julienrat/Norns_Fork/norns_fork_pcb/images/PXL_20220614_091723372.jpg

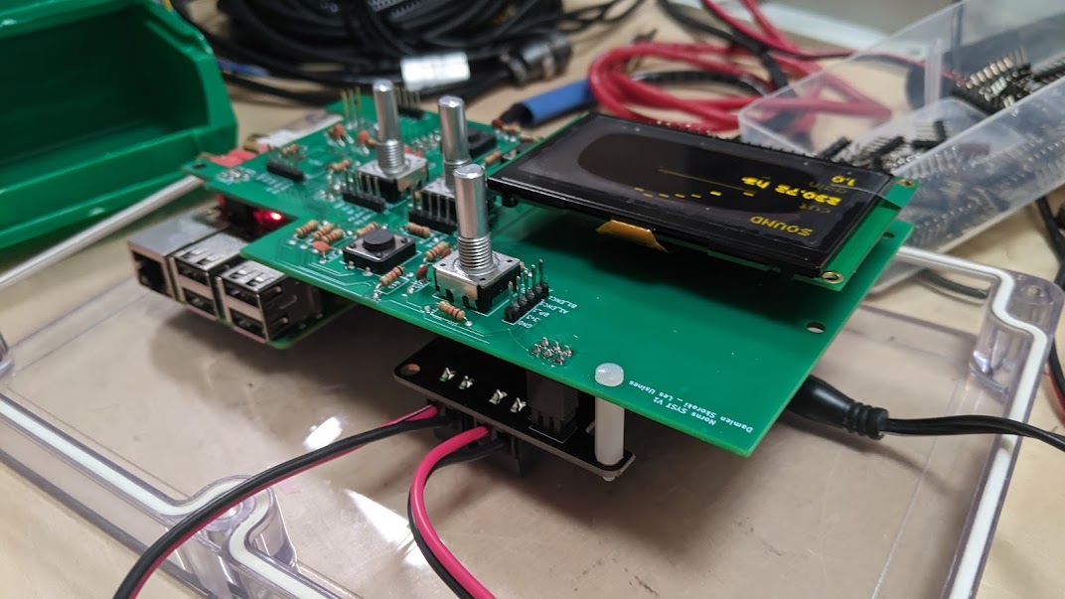
norns_fork_pcb/images/PXL_20220614_091723372.jpg
