julienrat/Norns_Fork/norns_fork_pcb/norns_EKO_kicad_sources/norns_eko_3.png

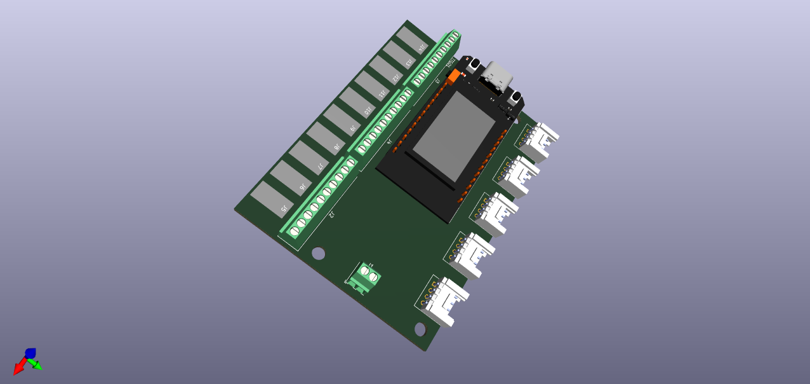
norns_fork_pcb/norns_EKO_kicad_sources/norns_eko_3.png
