julienrat/Norns_Fork/norns_fork_pcb/norns_EKO_kicad_sources/footprint/ttgo-tdisplay-kicad-master/microusb.SLDPRT

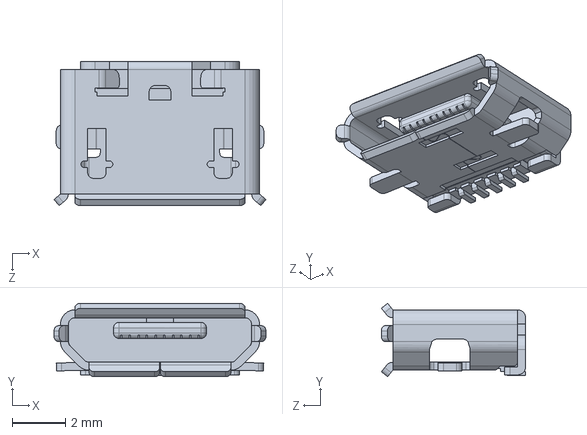
[picture p25: CAD file, 2022-07-06]
norns_fork_pcb/norns_EKO_kicad_sources/footprint/ttgo-tdisplay-kicad-master/microusb.SLDPRT
7.98 x 2.76 x 5.43 mm
