julienrat/Norns_Fork/norns_fork_pcb/norns_SYST_kicad_sources/edgecut/norns_fork-Edge_Cutsrnd.dxf

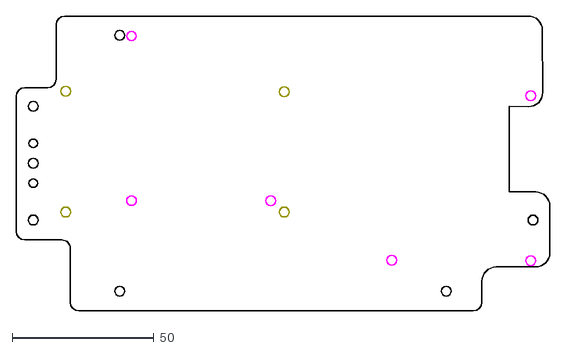
[picture p26: CAD file, 2022-07-06]
norns_fork_pcb/norns_SYST_kicad_sources/edgecut/norns_fork-Edge_Cutsrnd.dxf
187.9 x 103.8
