julienrat/Norns_Fork/norns_fork_pcb/norns_SYST_kicad_sources/footprint/Enc_Bourns_PEC11R-4015F-N0024/ecran.step

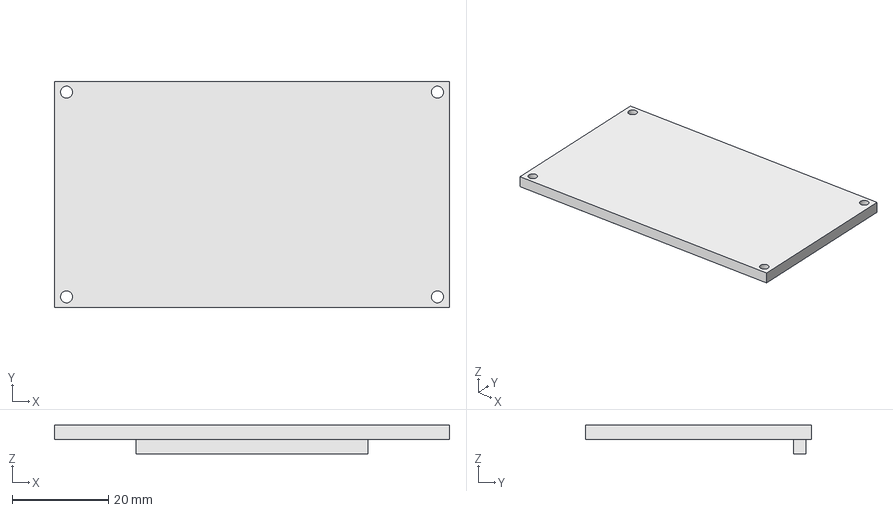
[picture p27: CAD file, 2022-06-02]
norns_fork_pcb/norns_SYST_kicad_sources/footprint/Enc_Bourns_PEC11R-4015F-N0024/ecran.step
82.0 x 47.0 x 6.00 mm
