julienrat/Norns_Fork/norns_fork_pcb/norns_SYST_kicad_sources/footprint/rb85p12_24.step

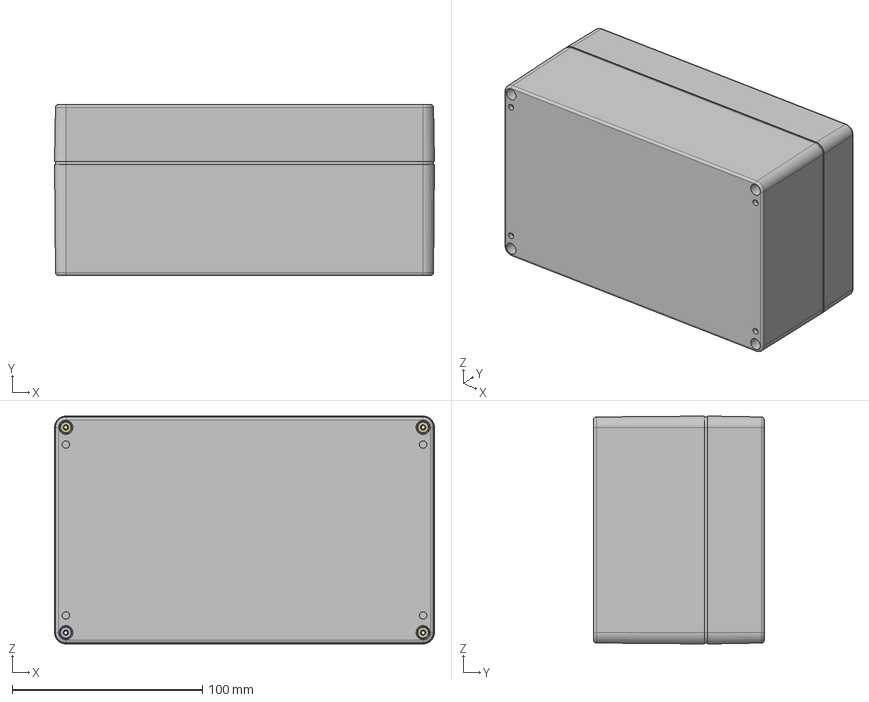
[picture p28: CAD file, 2022-07-06]
norns_fork_pcb/norns_SYST_kicad_sources/footprint/rb85p12_24.step
200.0 x 90.0 x 120.0 mm
RB85X24Y_RevA(Default)
RB85-X12Y_RevA
6102_4-40_threaded insert x 4
6032 4-40 Torx X 1.75_ Rev A x 4
8085 RB85 O Ring Rev A
