julienrat/Norns_Fork/3D_case/3D_case_syst_freecad/entretoises.FCStd

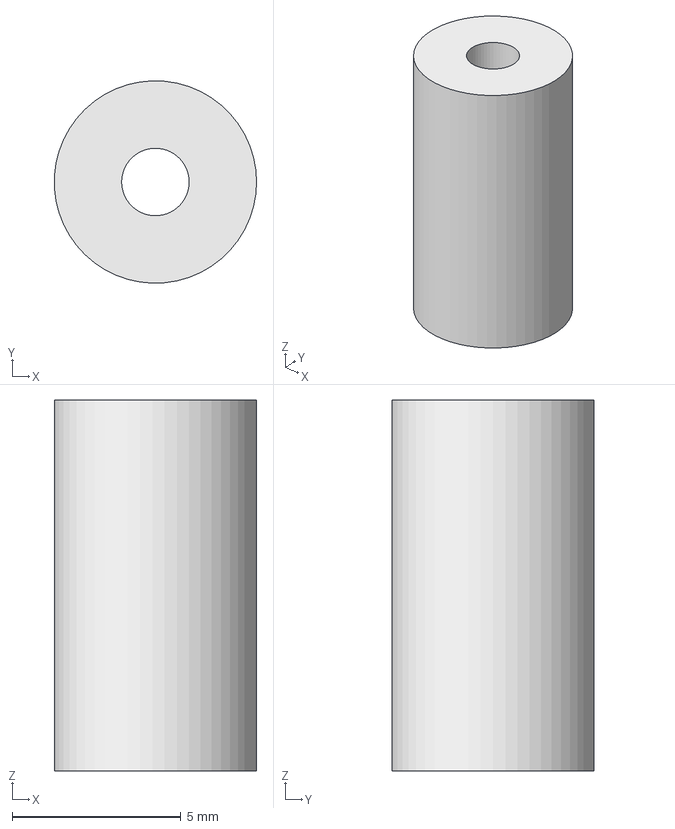
[picture p29: CAD file, 2022-06-15]
3D_case/3D_case_syst_freecad/entretoises.FCStd
5.99 x 6.00 x 11.0 mm
