julienrat/Norns_Fork/norns_fork_pcb/norns_SYST_kicad_sources/edgecut/#Fond boite.dxf

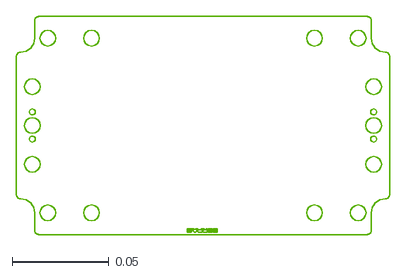
[picture p30: CAD file, 2022-07-06]
norns_fork_pcb/norns_SYST_kicad_sources/edgecut/#Fond boite.dxf
0.192 x 0.112
