julienrat/Norns_Fork/norns_fork_pcb/norns_SYST_kicad_sources/footprint/RASPBERRY PI 3.STEP

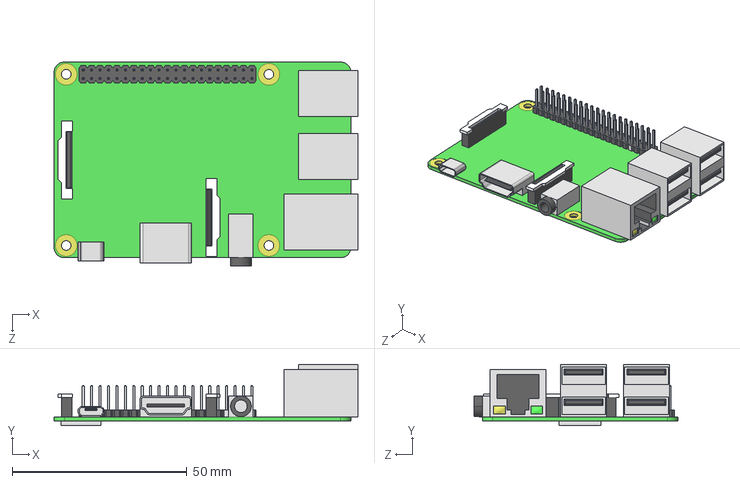
[picture p31: CAD file, 2022-06-15]
norns_fork_pcb/norns_SYST_kicad_sources/footprint/RASPBERRY PI 3.STEP
87.0 x 17.5 x 58.4 mm
