julienrat/Norns_Fork/norns_fork_pcb/norns_SYST_kicad_sources/edgecut/Norns_edgecut_final.dxf

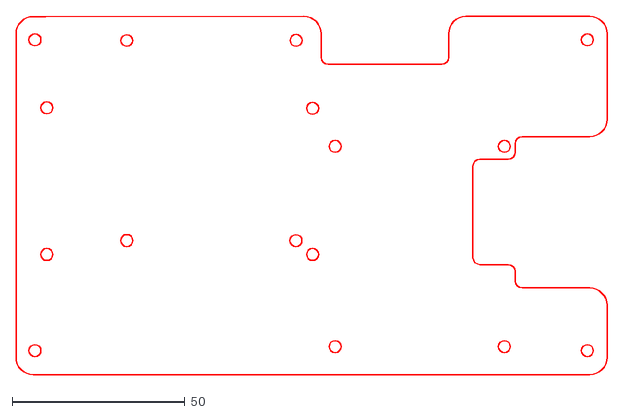
[picture p32: CAD file, 2022-07-01]
norns_fork_pcb/norns_SYST_kicad_sources/edgecut/Norns_edgecut_final.dxf
171.2 x 103.8
