julienrat/Norns_Fork/norns_fork_pcb/norns_SYST_kicad_sources/norns_fork.kicad_sch

## KiCad design norns_fork_pcb/norns_SYST_kicad_sources/norns_fork.kicad_sch (2022-07-01)

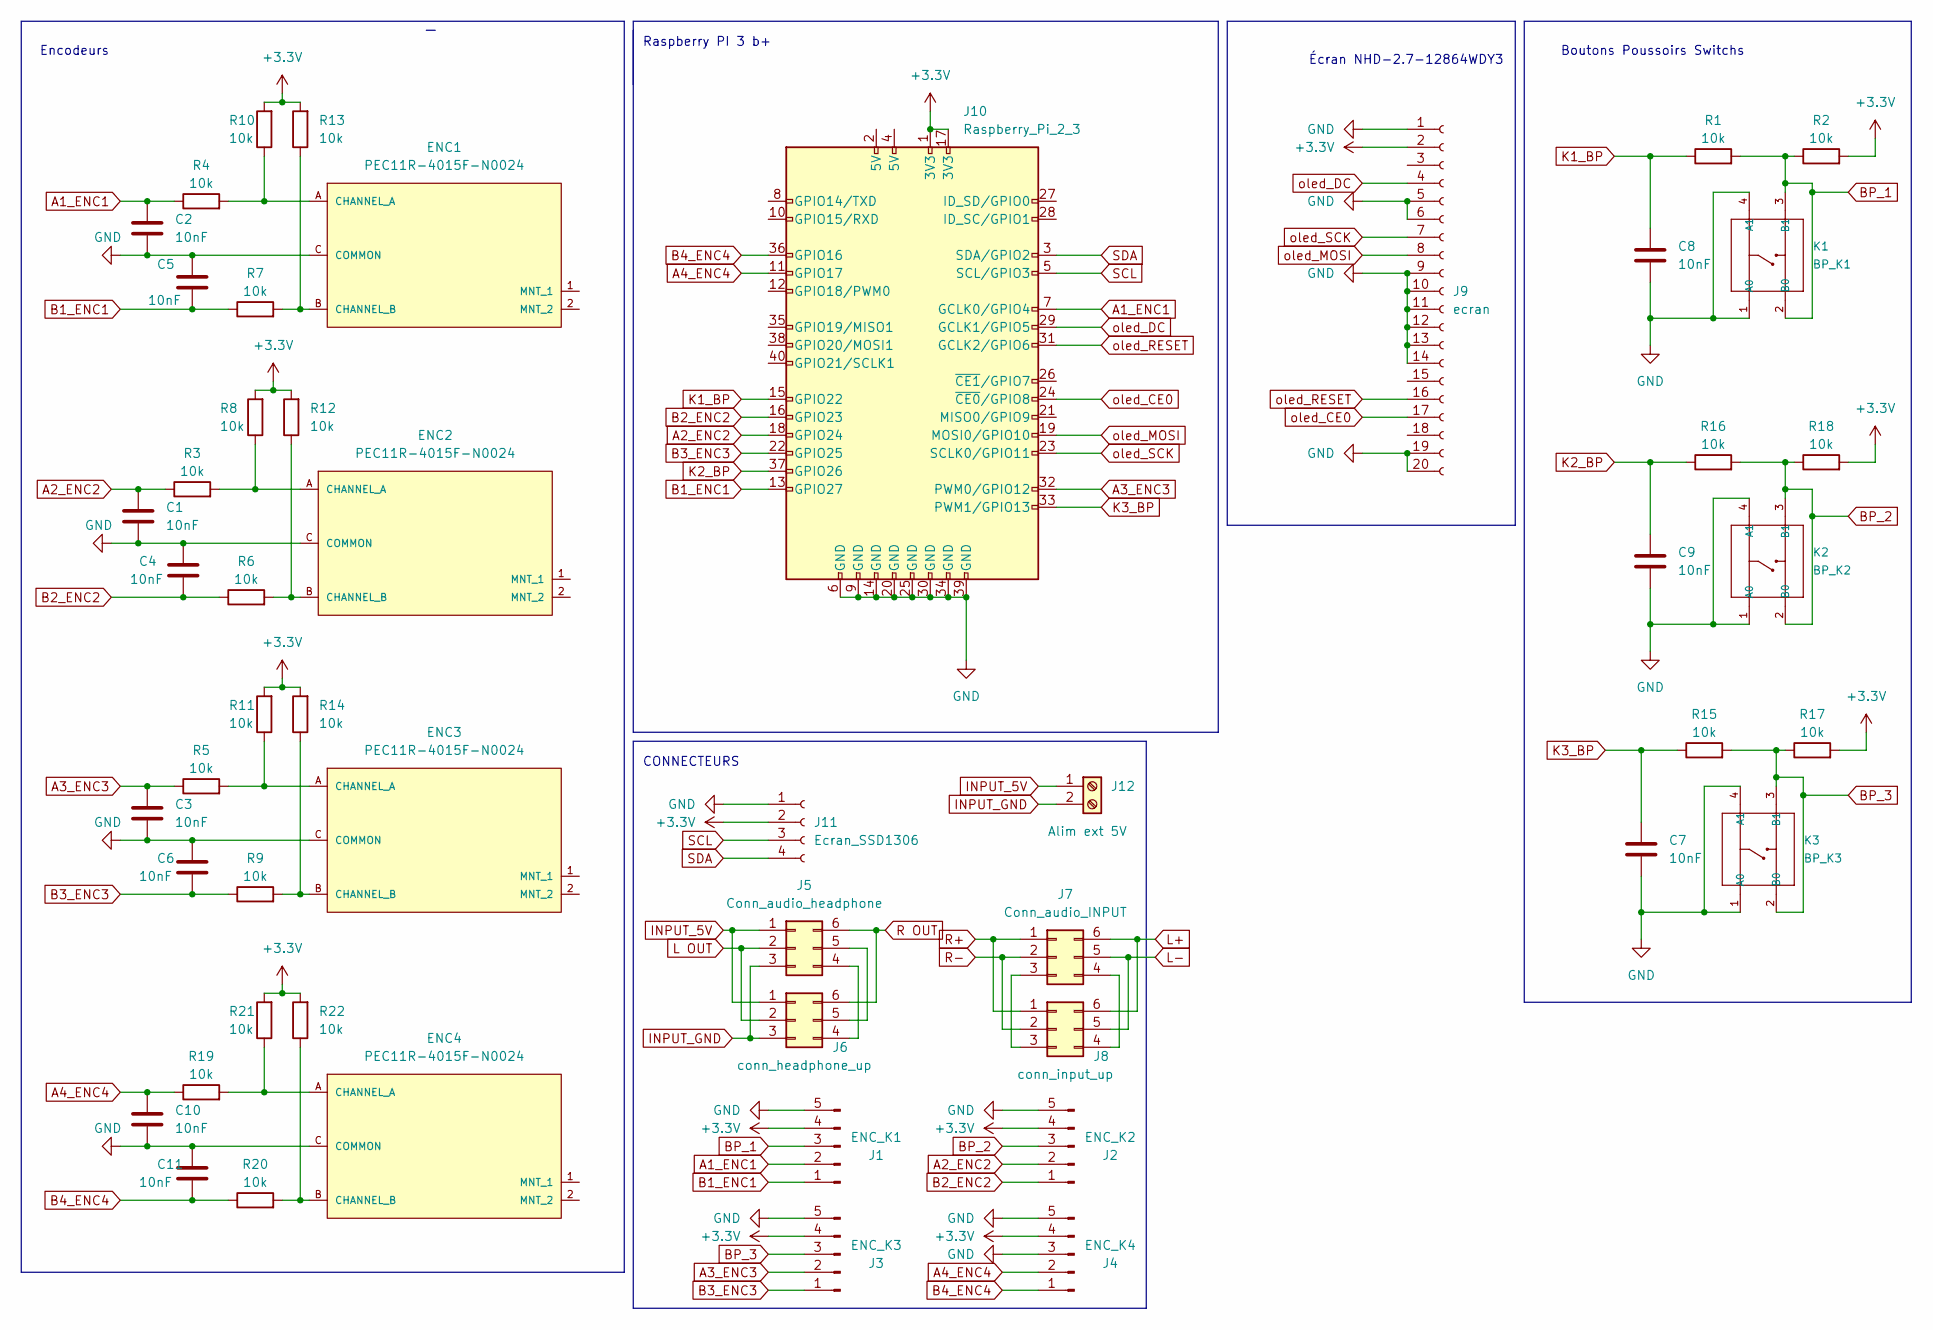
[picture p34: schematic norns_fork.kicad_sch]

Parts:
C1, C2, C3, C4, C5, C6, C7, C8, C9, C10, C11: 10nF; C_Disc_D4.3mm_W1.9mm_P5.00mm
ENC1, ENC2, ENC3, ENC4: PEC11R-4015F-N0024; Bourns-PEC11R-4015F-N0024-MFG; current rating 10mA; voltage rating DC 5V; mouser part number 652-PEC11R-4015F-N24; digikey description ROTARY ENCODER MECHANICAL 24PPR
J1: ENC_K1; PinHeader_1x05_P2.54mm_Vertical
J2: ENC_K2; PinHeader_1x05_P2.54mm_Vertical
J3: ENC_K3; PinHeader_1x05_P2.54mm_Vertical
J4: ENC_K4; PinHeader_1x05_P2.54mm_Vertical
J5: Conn_audio_headphone; PinSocket_2x03_P2.54mm_Vertical
J6: conn_headphone_up; PinSocket_2x03_P2.54mm_Vertical
J7: Conn_audio_INPUT; PinSocket_2x03_P2.54mm_Vertical
J8: conn_input_up; PinSocket_2x03_P2.54mm_Vertical
J9: ecran; PinHeader_1x20_P2.54mm_Vertical
J10: Raspberry_Pi_2_3; PinHeader_2x20_P2.54mm_Vertical
J11: Ecran_SSD1306; PinSocket_1x04_P2.54mm_Vertical
J12: Alim ext 5V; TerminalBlock_Altech_AK300-2_P5.00mm
K1: BP_K1; SW_PUSH-12mm_Wuerth-430476085716
K2: BP_K2; SW_PUSH-12mm_Wuerth-430476085716
K3: BP_K3; SW_PUSH-12mm_Wuerth-430476085716
R1, R2, R3, R4, R5, R6, R7, R8, R9, R10, R11, R12, R13, R14, R15, R16, R17, R18, R19, R20, R21, R22: 10k; R_Axial_DIN0207_L6.3mm_D2.5mm_P10.16mm_Horizontal

Connections:
+3.3V: J1.4, J2.4, J3.4, J4.4, J9.2, J10.1 (3V3), J10.17 (3V3), J11.2, R2.2, R8.2, R10.2, R11.2, R12.2, R13.2, R14.2, R17.2, R18.2, R21.2, R22.2
A1_ENC1: C2.2, J1.2, J10.7 (GCLK0/GPIO4), R4.1
A2_ENC2: C1.2, J2.2, J10.18 (GPIO24), R3.1
A3_ENC3: C3.2, J3.2, J10.32 (PWM0/GPIO12), R5.1
A4_ENC4: C10.2, J4.2, J10.11 (GPIO17), R19.1
B1_ENC1: C5.1, J1.1, J10.13 (GPIO27), R7.1
B2_ENC2: C4.1, J2.1, J10.16 (GPIO23), R6.1
B3_ENC3: C6.1, J3.1, J10.22 (GPIO25), R9.1
B4_ENC4: C11.1, J4.1, J10.36 (GPIO16), R20.1
BP_1: J1.3, K1.2 (B0), K1.3 (B1), R1.2, R2.1
BP_2: J2.3, K2.2 (B0), K2.3 (B1), R16.2, R18.1
BP_3: J3.3, K3.2 (B0), K3.3 (B1), R15.2, R17.1
GND: C1.1, C2.1, C3.1, C4.2, C5.2, C6.2, C7.1, C8.1, C9.1, C10.1, C11.2, ENC1.C (COMMON), ENC2.C (COMMON), ENC3.C (COMMON), ENC4.C (COMMON), J1.5, J2.5, J3.5, J4.3, J4.5, J9.1, J9.5, J9.6, J9.9, J9.10, J9.11, J9.12, J9.13, J9.14, J9.19, J9.20, J10.6 (GND), J10.9 (GND), J10.14 (GND), J10.20 (GND), J10.25 (GND), J10.30 (GND), J10.34 (GND), J10.39 (GND), J11.1, K1.1 (A0), K1.4 (A1), K2.1 (A0), K2.4 (A1), K3.1 (A0), K3.4 (A1)
INPUT_5V: J5.1, J6.1, J12.1
INPUT_GND: J5.3, J6.3, J12.2
K1_BP: C8.2, J10.15 (GPIO22), R1.1
K2_BP: C9.2, J10.37 (GPIO26), R16.1
K3_BP: C7.2, J10.33 (PWM1/GPIO13), R15.1
L OUT: J5.2, J6.2
L+: J7.6, J8.6
L-: J7.5, J8.5
unnamed: ENC1.A (CHANNEL_A), R4.2, R10.1
unnamed: ENC1.B (CHANNEL_B), R7.2, R13.1
unnamed: ENC2.A (CHANNEL_A), R3.2, R8.1
unnamed: ENC2.B (CHANNEL_B), R6.2, R12.1
unnamed: ENC3.A (CHANNEL_A), R5.2, R11.1
unnamed: ENC3.B (CHANNEL_B), R9.2, R14.1
unnamed: ENC4.A (CHANNEL_A), R19.2, R21.1
unnamed: ENC4.B (CHANNEL_B), R20.2, R22.1
unnamed: J5.4, J6.4
unnamed: J5.5, J6.5
unnamed: J7.3, J8.3
unnamed: J7.4, J8.4
R OUT: J5.6, J6.6
R+: J7.1, J8.1
R-: J7.2, J8.2
SCL: J10.5 (SCL/GPIO3), J11.3
SDA: J10.3 (SDA/GPIO2), J11.4
oled_CE0: J9.17, J10.24 (~CE0/GPIO8)
oled_DC: J9.4, J10.29 (GCLK1/GPIO5)
oled_MOSI: J9.8, J10.19 (MOSI0/GPIO10)
oled_RESET: J9.16, J10.31 (GCLK2/GPIO6)
oled_SCK: J9.7, J10.23 (SCLK0/GPIO11)

Notes on the sheet:
Encodeurs
CONNECTEURS
Écran NHD-2.7-12864WDY3
Raspberry PI 3 b+
Boutons Poussoirs Switchs
